tikinson/ToadsTempest/Toad'sTempest.kicad_sch

## KiCad design Toad'sTempest.kicad_sch (2024-09-08)

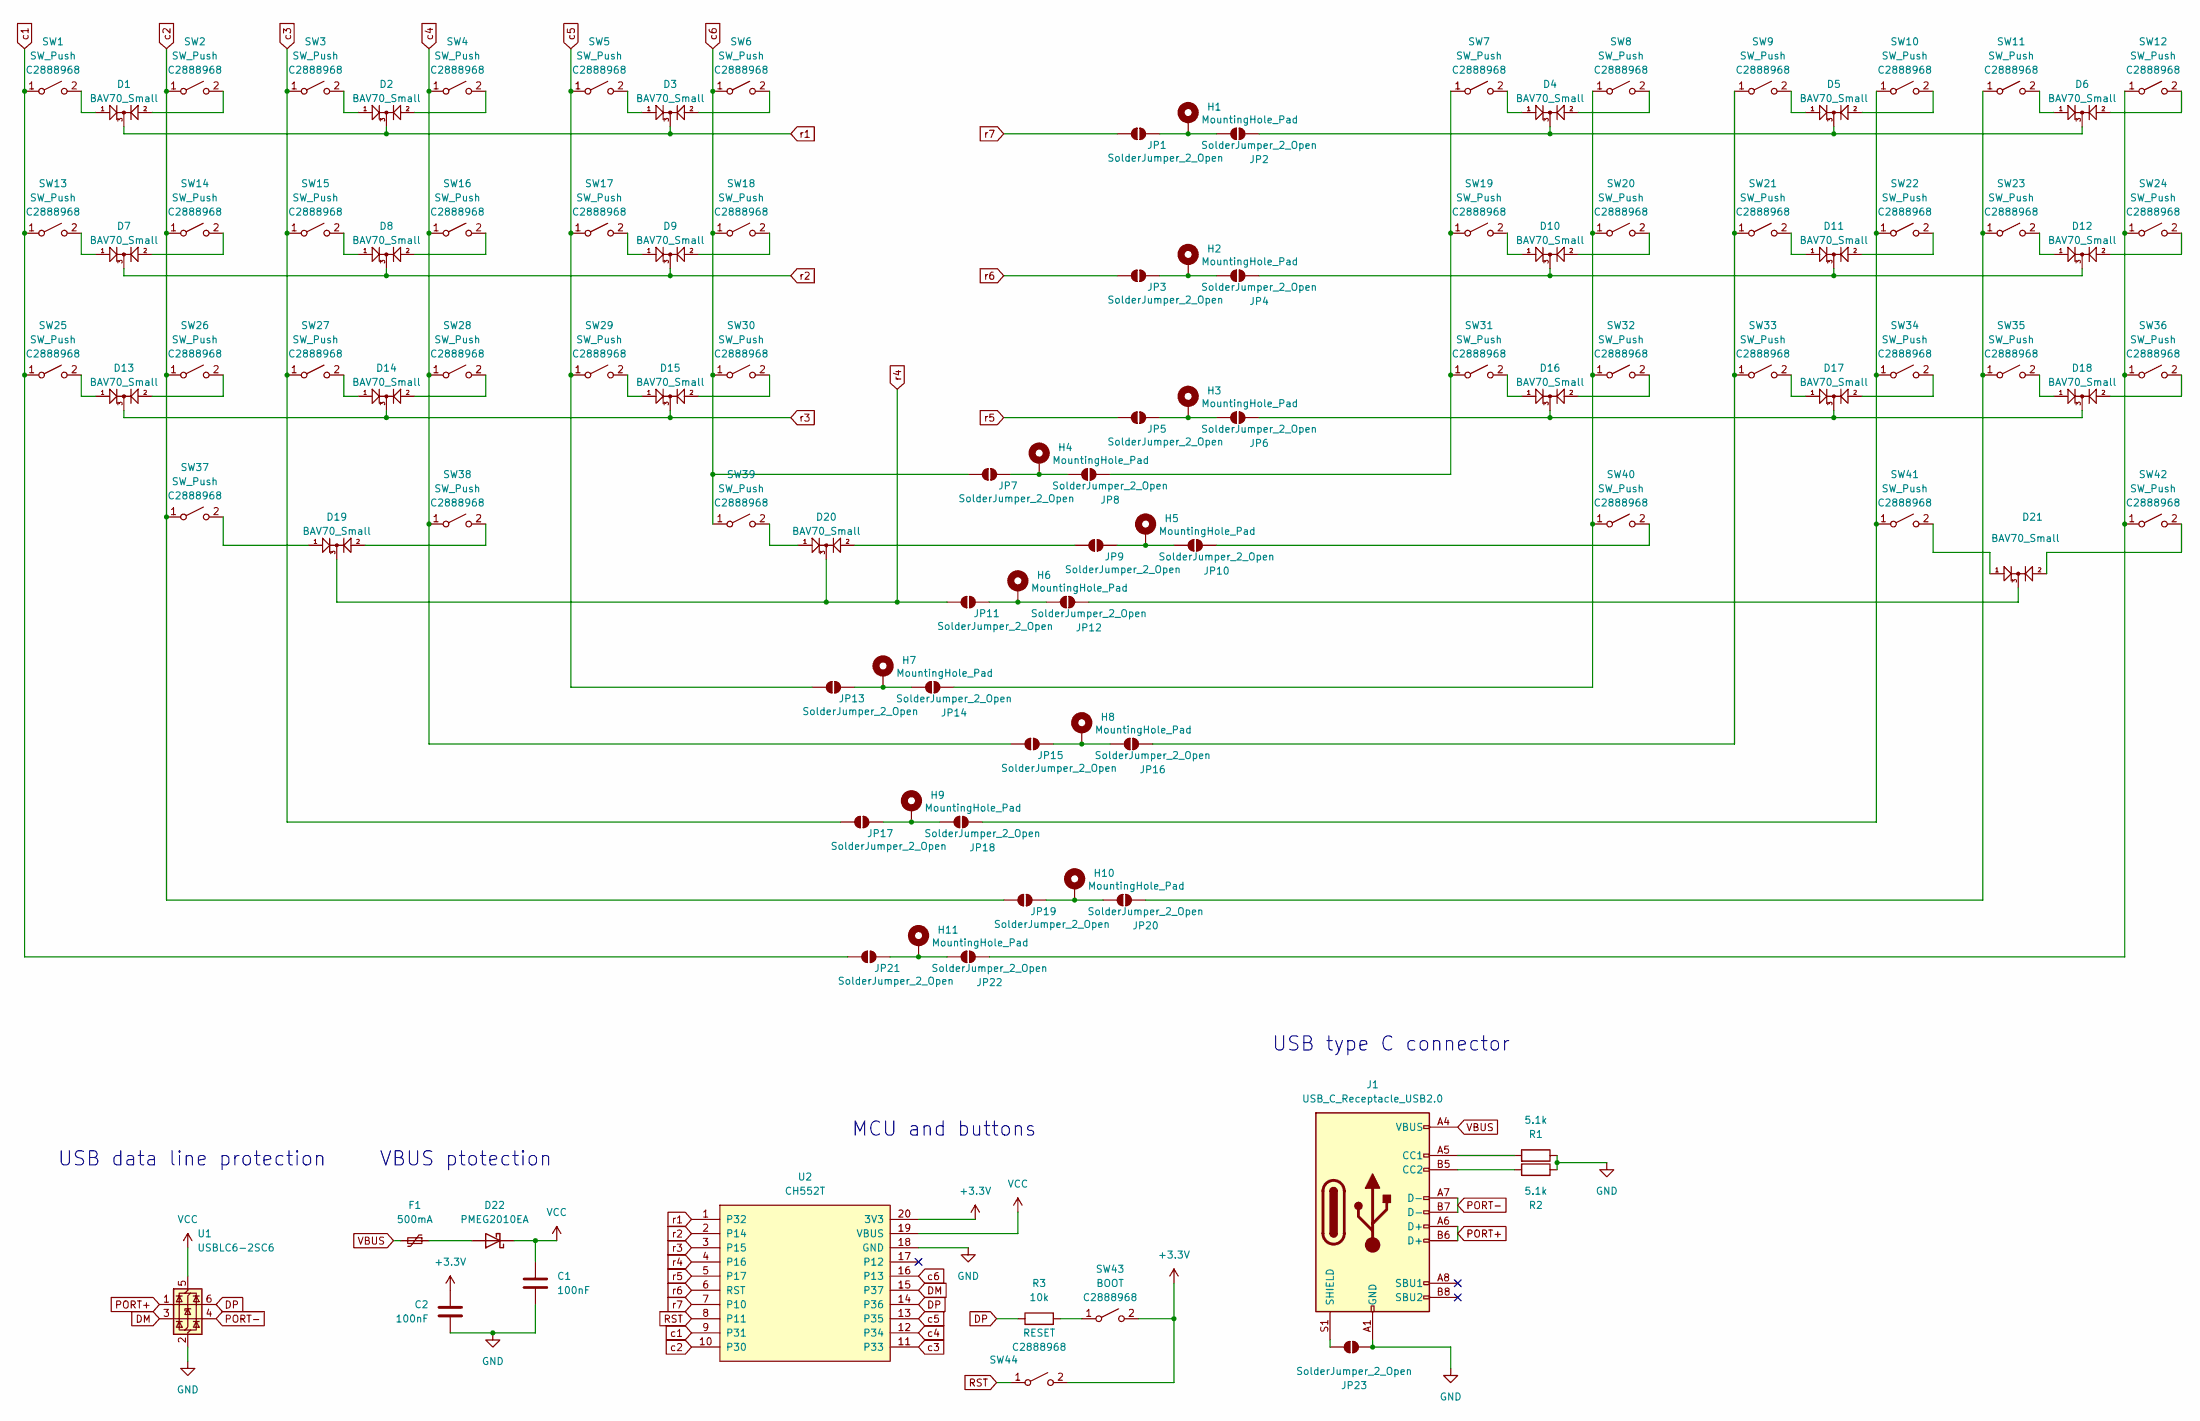
[picture p10: schematic Toad'sTempest.kicad_sch]

Parts:
C1, C2: 100nF; C_0402_1005Metric_Pad0.74x0.62mm_HandSolder; LCSC C1525
D1, D2, D3, D4, D5, D6, D7, D8, D9, D10, D11, D12, D13, D14, D15, D16, D17, D18, D19, D20, D21: BAV70_Small; SOT-23_Handsoldering
D22: PMEG2010EA; D_0402_1005Metric_Pad0.77x0.64mm_HandSolder; LCSC C2837790
F1: 500mA; Fuse_0402_1005Metric_Pad0.77x0.64mm_HandSolder; LCSC C210357
H1, H2, H3, H4, H5, H6, H7, H8, H9, H10, H11: MountingHole_Pad; castellated pad
J1: USB_C_Receptacle_USB2.0; USB_C_Receptacle_HRO_TYPE-C-31-M-12; JLCPCB_CORRECTION 0; -1.35; 0
JP1, JP2, JP3, JP4, JP5, JP6, JP7, JP8, JP9, JP10, JP11, JP12, JP13, JP14, JP15, JP16, JP17, JP18, JP19, JP20, JP21, JP22, JP23: SolderJumper_2_Open; SolderJumper-2_P1.3mm_Open_TrianglePad1.0x1.5mm
R1, R2: 5.1k; R_0402_1005Metric_Pad0.72x0.64mm_HandSolder; LCSC C25905
R3: 10k; R_0402_1005Metric_Pad0.72x0.64mm_HandSolder; LCSC C25744
SW1, SW2, SW3, SW4, SW5, SW6, SW7, SW8, SW9, SW10, SW11, SW12, SW13, SW14, SW15, SW16, SW17, SW18, SW19, SW20, SW21, SW22, SW23, SW24, SW25, SW26, SW27, SW28, SW29, SW30, SW31, SW32, SW33, SW34, SW35, SW36, SW37, SW38, SW39, SW40, SW41, SW42: SW_Push; BZCN-tsc003; LCSC Part C2888968
SW43: BOOT; BZCN-tsc003; LCSC C115357
SW44: RESET; BZCN-tsc003; LCSC C115357
U1: USBLC6-2SC6; SOT-23-6; JLCPCB_CORRECTION 0; 0; 270
U2: CH552T; TSSOP-20_4.4x6.5mm_P0.65mm; LCSC C111367

Connections:
+3.3V: C2.1, SW43.2 (B), SW44.2 (B), U2.20 (3V3)
DM: U1.3 (I/O2), U2.15 (P37)
DP: R3.1, U1.6 (I/O1), U2.14 (P36)
GND: C1.2, C2.2, J1.A1 (GND), J1.A12 (GND), J1.B1 (GND), J1.B12 (GND), JP23.2 (B), R1.1, R2.1, U1.2 (GND), U2.18 (GND)
unnamed: D1.1 (A1), SW1.2 (B)
unnamed: D1.2 (A2), SW2.2 (B)
unnamed: D2.1 (A1), SW3.2 (B)
unnamed: D2.2 (A2), SW4.2 (B)
unnamed: D3.1 (A1), SW5.2 (B)
unnamed: D3.2 (A2), SW6.2 (B)
unnamed: D4.1 (A1), SW7.2 (B)
unnamed: D4.2 (A2), SW8.2 (B)
unnamed: D4.3 (K), D5.3 (K), D6.3 (K), JP2.2 (B)
unnamed: D5.1 (A1), SW9.2 (B)
unnamed: D5.2 (A2), SW10.2 (B)
unnamed: D6.1 (A1), SW11.2 (B)
unnamed: D6.2 (A2), SW12.2 (B)
unnamed: D7.1 (A1), SW13.2 (B)
unnamed: D7.2 (A2), SW14.2 (B)
unnamed: D8.1 (A1), SW15.2 (B)
unnamed: D8.2 (A2), SW16.2 (B)
unnamed: D9.1 (A1), SW17.2 (B)
unnamed: D9.2 (A2), SW18.2 (B)
unnamed: D10.1 (A1), SW19.2 (B)
unnamed: D10.2 (A2), SW20.2 (B)
unnamed: D10.3 (K), D11.3 (K), D12.3 (K), JP4.2 (B)
unnamed: D11.1 (A1), SW21.2 (B)
unnamed: D11.2 (A2), SW22.2 (B)
unnamed: D12.1 (A1), SW23.2 (B)
unnamed: D12.2 (A2), SW24.2 (B)
unnamed: D13.1 (A1), SW25.2 (B)
unnamed: D13.2 (A2), SW26.2 (B)
unnamed: D14.1 (A1), SW27.2 (B)
unnamed: D14.2 (A2), SW28.2 (B)
unnamed: D15.1 (A1), SW29.2 (B)
unnamed: D15.2 (A2), SW30.2 (B)
unnamed: D16.1 (A1), SW31.2 (B)
unnamed: D16.2 (A2), SW32.2 (B)
unnamed: D16.3 (K), D17.3 (K), D18.3 (K), JP6.2 (B)
unnamed: D17.1 (A1), SW33.2 (B)
unnamed: D17.2 (A2), SW34.2 (B)
unnamed: D18.1 (A1), SW35.2 (B)
unnamed: D18.2 (A2), SW36.2 (B)
unnamed: D19.1 (A1), SW37.2 (B)
unnamed: D19.2 (A2), SW38.2 (B)
unnamed: D20.1 (A1), SW39.2 (B)
unnamed: D20.2 (A2), JP9.1 (A)
unnamed: D21.1 (A1), SW41.2 (B)
unnamed: D21.2 (A2), SW42.2 (B)
unnamed: D21.3 (K), JP12.2 (B)
unnamed: D22.2 (A), F1.1
unnamed: H1.1, JP1.2 (B), JP2.1 (A)
unnamed: H2.1, JP3.2 (B), JP4.1 (A)
unnamed: H3.1, JP5.2 (B), JP6.1 (A)
unnamed: H4.1, JP7.2 (B), JP8.1 (A)
unnamed: H5.1, JP9.2 (B), JP10.1 (A)
unnamed: H6.1, JP11.2 (B), JP12.1 (A)
unnamed: H7.1, JP13.2 (B), JP14.1 (A)
unnamed: H8.1, JP15.2 (B), JP16.1 (A)
unnamed: H9.1, JP17.2 (B), JP18.1 (A)
unnamed: H10.1, JP19.2 (B), JP20.1 (A)
unnamed: H11.1, JP21.2 (B), JP22.1 (A)
unnamed: J1.A5 (CC1), R1.2
unnamed: J1.B5 (CC2), R2.2
unnamed: J1.S1 (SHIELD), JP23.1 (A)
unnamed: JP8.2 (B), SW7.1 (A), SW19.1 (A), SW31.1 (A)
unnamed: JP10.2 (B), SW40.2 (B)
unnamed: JP14.2 (B), SW8.1 (A), SW20.1 (A), SW32.1 (A), SW40.1 (A)
unnamed: JP16.2 (B), SW9.1 (A), SW21.1 (A), SW33.1 (A)
unnamed: JP18.2 (B), SW10.1 (A), SW22.1 (A), SW34.1 (A), SW41.1 (A)
unnamed: JP20.2 (B), SW11.1 (A), SW23.1 (A), SW35.1 (A)
unnamed: JP22.2 (B), SW12.1 (A), SW24.1 (A), SW36.1 (A), SW42.1 (A)
unnamed: R3.2, SW43.1 (A)
PORT+: J1.A6 (D+), J1.B6 (D+), U1.1 (I/O1)
PORT-: J1.A7 (D-), J1.B7 (D-), U1.4 (I/O2)
RST: SW44.1 (A), U2.8 (P11)
VBUS: F1.2, J1.A4 (VBUS), J1.A9 (VBUS), J1.B4 (VBUS), J1.B9 (VBUS)
VCC: C1.1, D22.1 (K), U1.5 (VBUS), U2.19 (VBUS)
c1: JP21.1 (A), SW1.1 (A), SW13.1 (A), SW25.1 (A), U2.9 (P31)
c2: JP19.1 (A), SW2.1 (A), SW14.1 (A), SW26.1 (A), SW37.1 (A), U2.10 (P30)
c3: JP17.1 (A), SW3.1 (A), SW15.1 (A), SW27.1 (A), U2.11 (P33)
c4: JP15.1 (A), SW4.1 (A), SW16.1 (A), SW28.1 (A), SW38.1 (A), U2.12 (P34)
c5: JP13.1 (A), SW5.1 (A), SW17.1 (A), SW29.1 (A), U2.13 (P35)
c6: JP7.1 (A), SW6.1 (A), SW18.1 (A), SW30.1 (A), SW39.1 (A), U2.16 (P13)
r1: D1.3 (K), D2.3 (K), D3.3 (K), U2.1 (P32)
r2: D7.3 (K), D8.3 (K), D9.3 (K), U2.2 (P14)
r3: D13.3 (K), D14.3 (K), D15.3 (K), U2.3 (P15)
r4: D19.3 (K), D20.3 (K), JP11.1 (A), U2.4 (P16)
r5: JP5.1 (A), U2.5 (P17)
r6: JP3.1 (A), U2.6 (RST)
r7: JP1.1 (A), U2.7 (P10)

Notes on the sheet:
USB data line protection
MCU and buttons
USB type C connector
VBUS ptotection
